EpicKarl/mDesign/Doku/HutschienengehaeuseCADDaten/ESP_Gehaeuse_Buttom.jpg

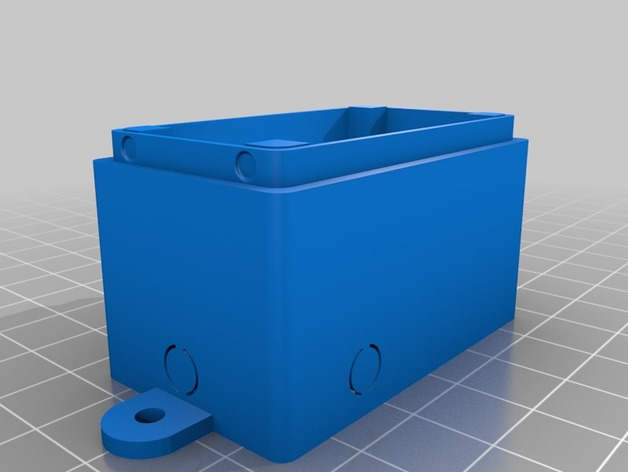
Doku/HutschienengehaeuseCADDaten/ESP_Gehaeuse_Buttom.jpg
