EpicKarl/mDesign/Doku/HutschienengehaeuseCADDaten/ESP_Gehaeuse_Zusammenbau1.jpeg

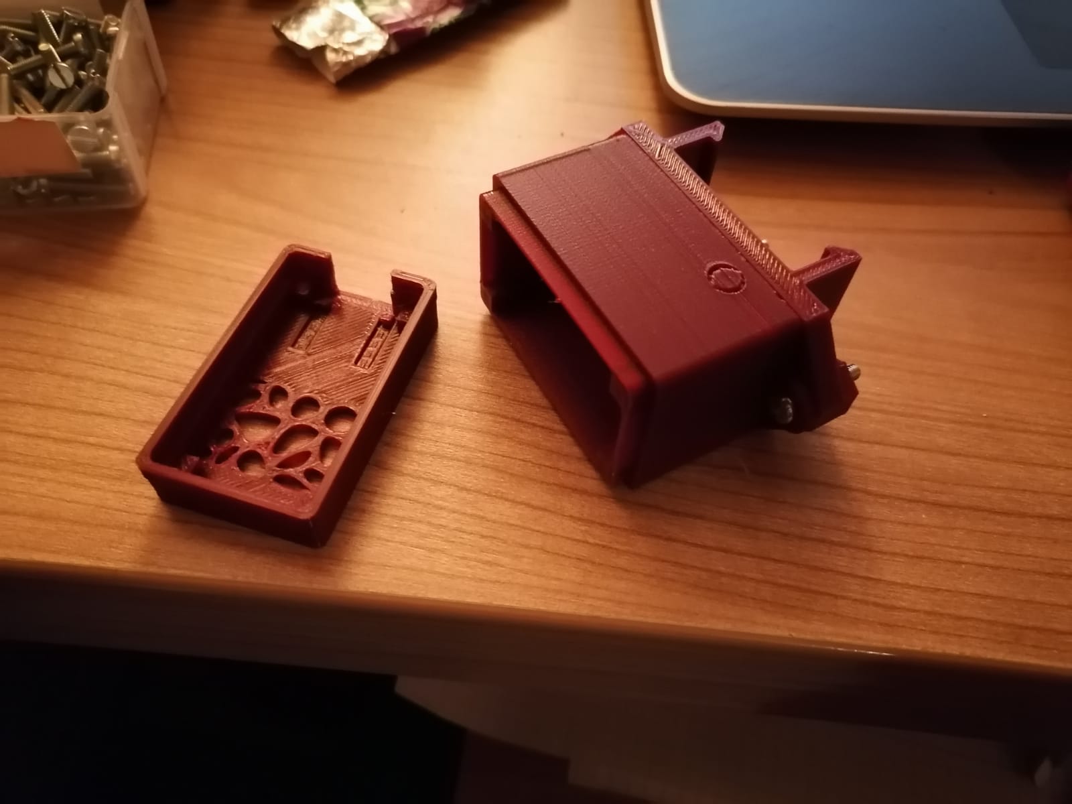
Doku/HutschienengehaeuseCADDaten/ESP_Gehaeuse_Zusammenbau1.jpeg
