EpicKarl/mDesign/Doku/TeildokumentationGUI/GUI_Manuel.jpg

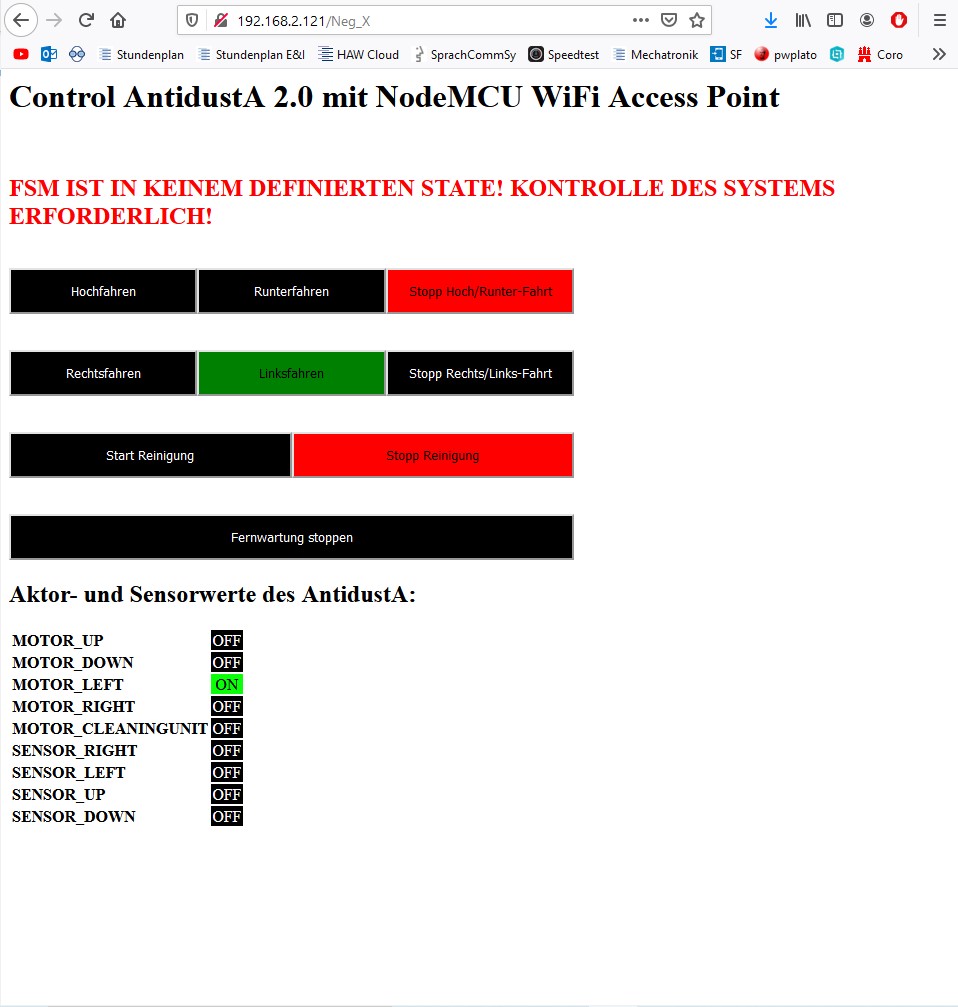
Doku/TeildokumentationGUI/GUI_Manuel.jpg
